shaashvats/litho_machining_m27x1.5/img1.jpeg

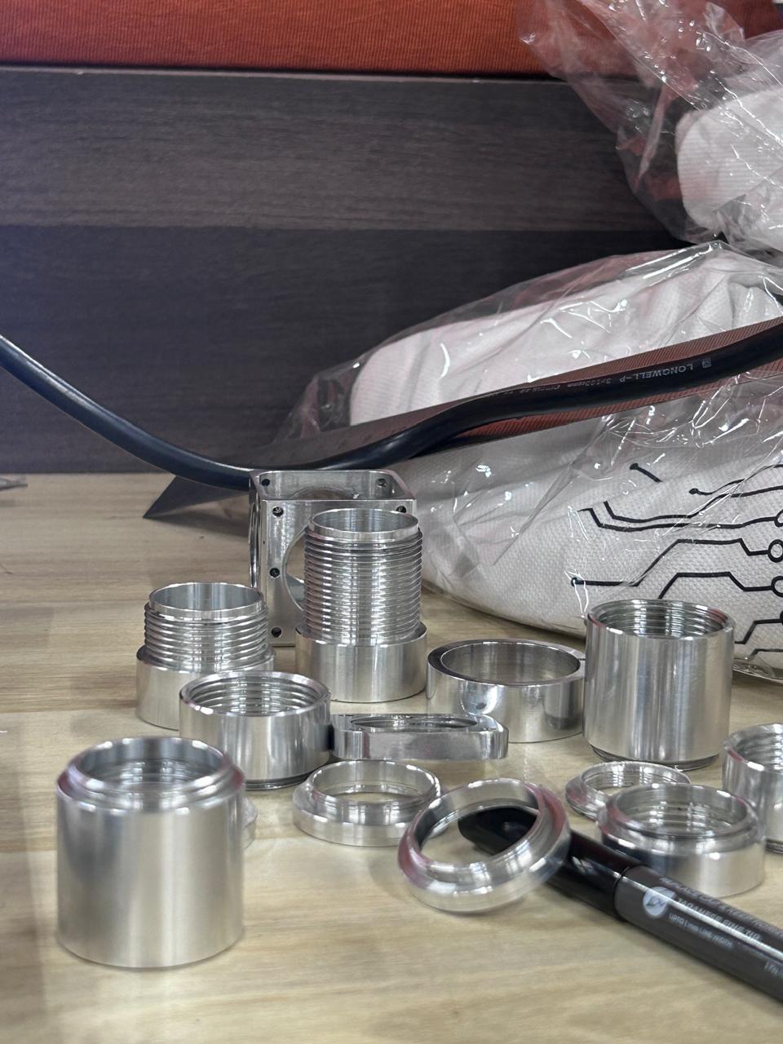
img1.jpeg
