shaashvats/litho_machining_m27x1.5/15_CM1_DCH/CM1-DCH-top.STEP

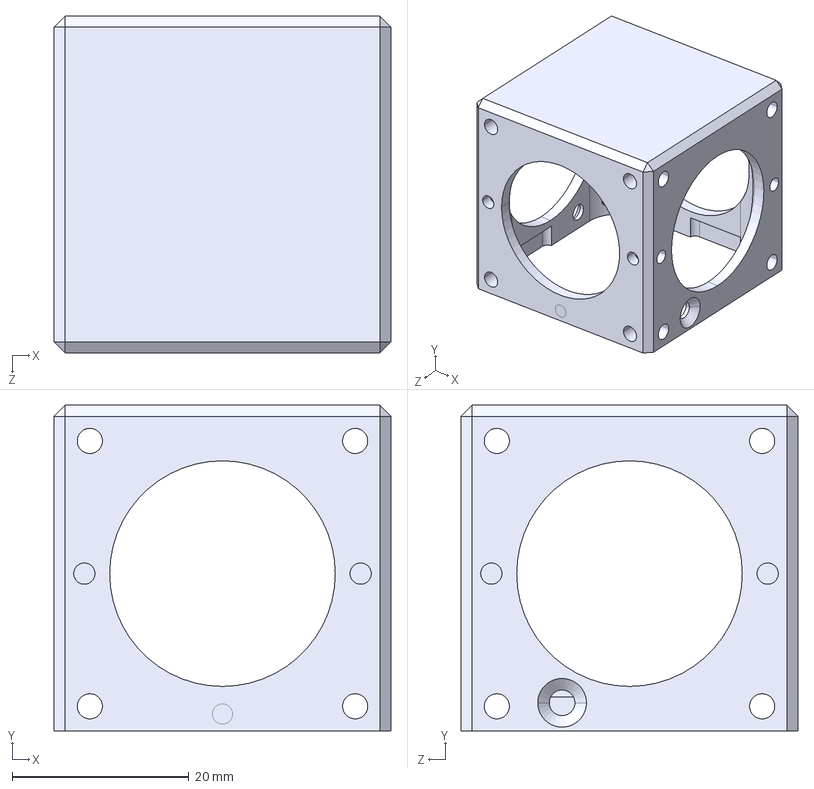
[picture p17: CAD file, 2026-01-12]
15_CM1_DCH/CM1-DCH-top.STEP
38.1 x 36.8 x 38.1 mm
