shaashvats/litho_machining_m27x1.5/15_CM1_DCH/CM1-DCH-Solidworks.sldprt

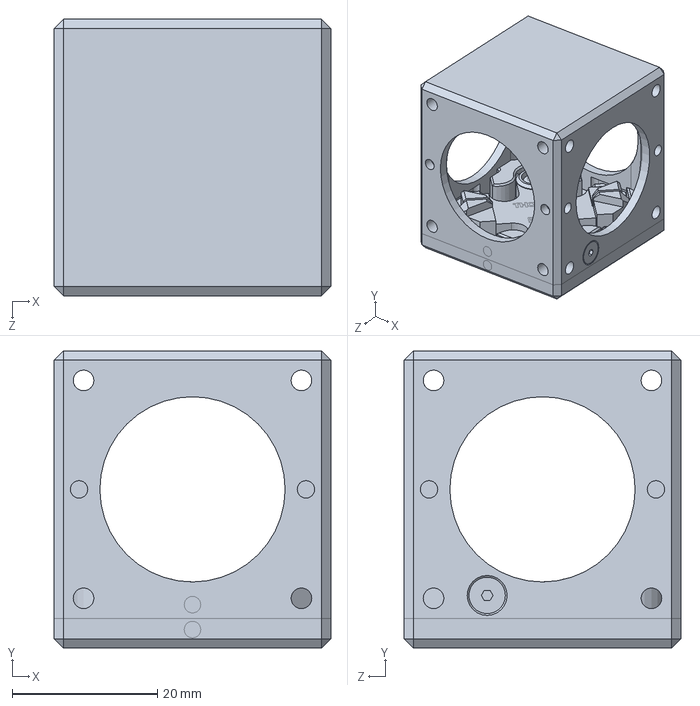
[picture p18: CAD file, 2026-01-12]
15_CM1_DCH/CM1-DCH-Solidworks.sldprt
38.1 x 40.9 x 38.1 mm
