shaashvats/litho_machining_m27x1.5/15_CM1_DCH/CM1-DCH-bottom.STEP

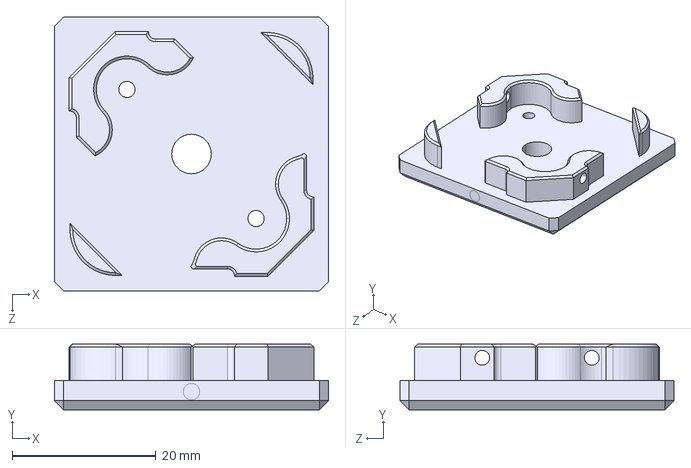
[picture p19: CAD file, 2026-01-12]
15_CM1_DCH/CM1-DCH-bottom.STEP
38.1 x 9.14 x 38.1 mm
