shaashvats/litho_machining_m27x1.5/15_CM1_DCH/CM1-DCH-splitterbase.STEP

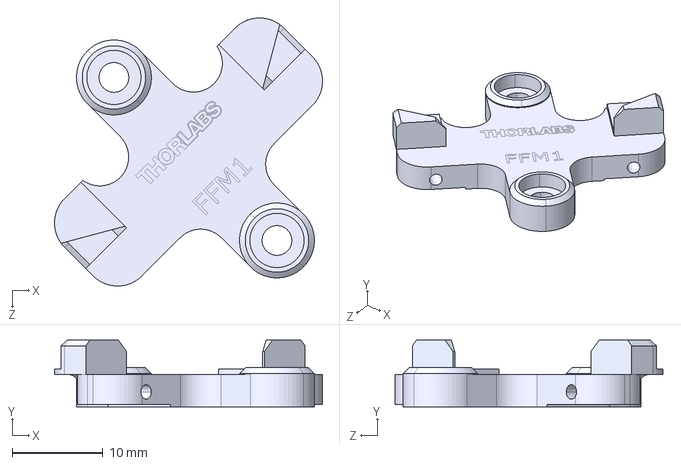
[picture p20: CAD file, 2026-01-12]
15_CM1_DCH/CM1-DCH-splitterbase.STEP
29.5 x 7.37 x 29.5 mm
